IamGPIO/BitHalo-201-204-Bitaxe/Optional DC Jack/DC Jack Rear.png

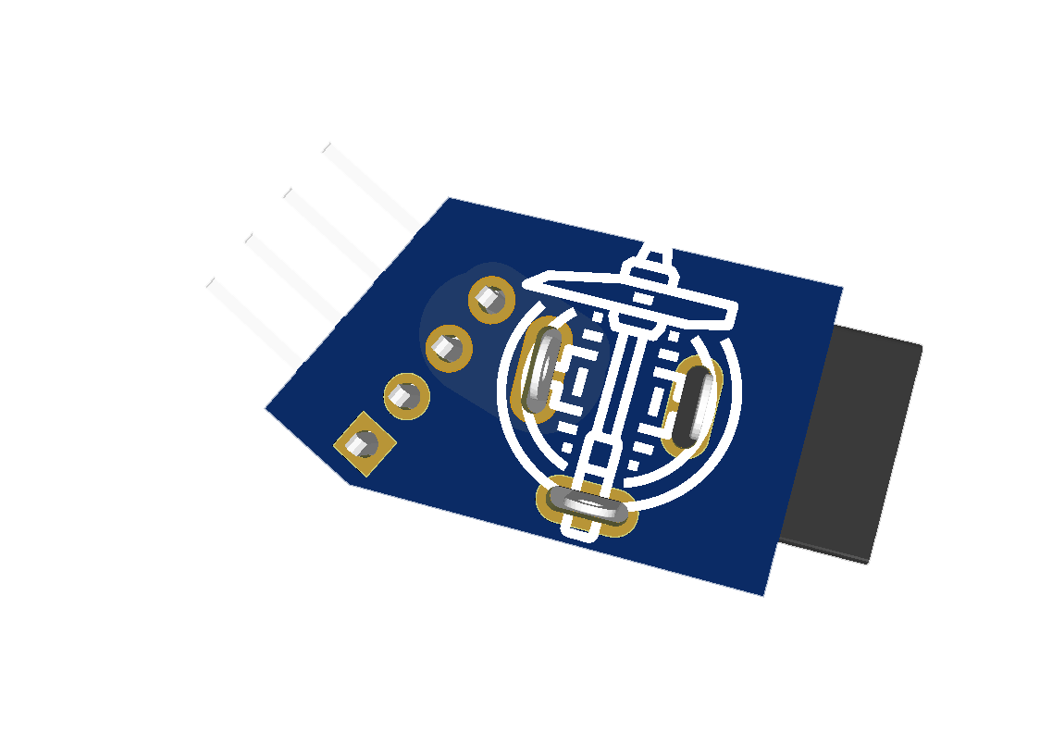
Optional DC Jack/DC Jack Rear.png
